JackSuuu/SDP-project-Haloassist/poster/SDP_poster.png

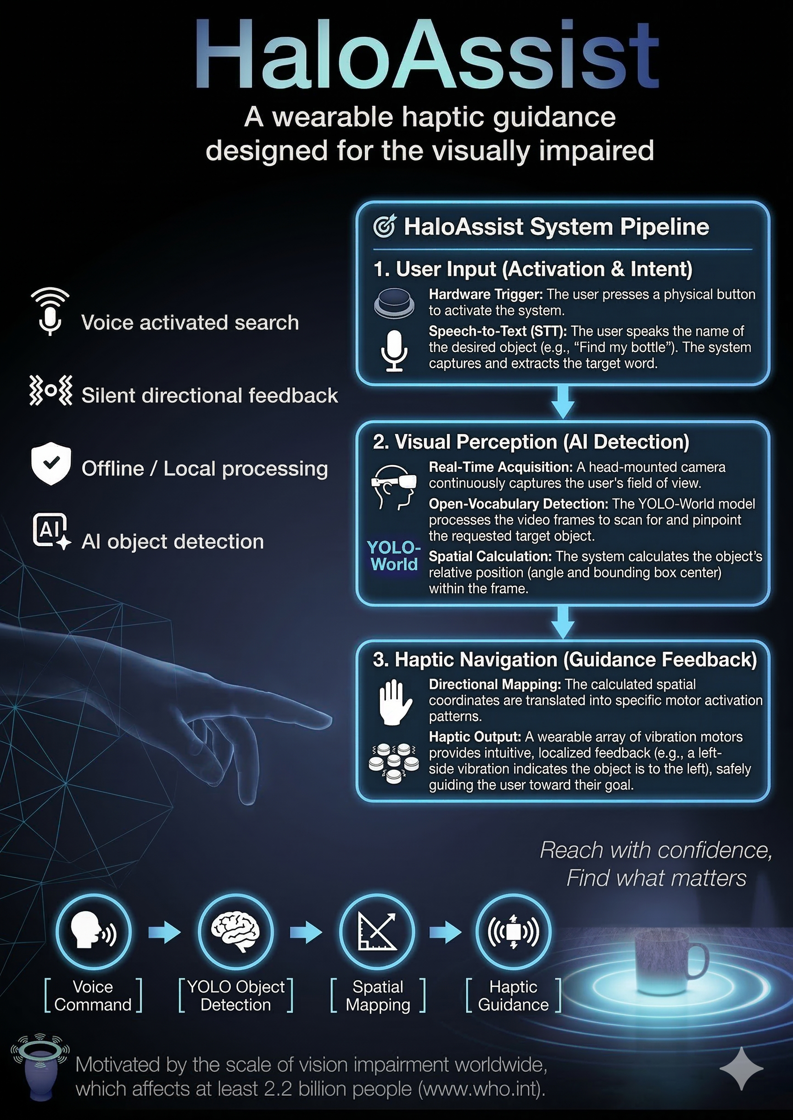
poster/SDP_poster.png
