JackSuuu/SDP-project-Haloassist/Screenshot at 2026-02-09 15-01-05.png

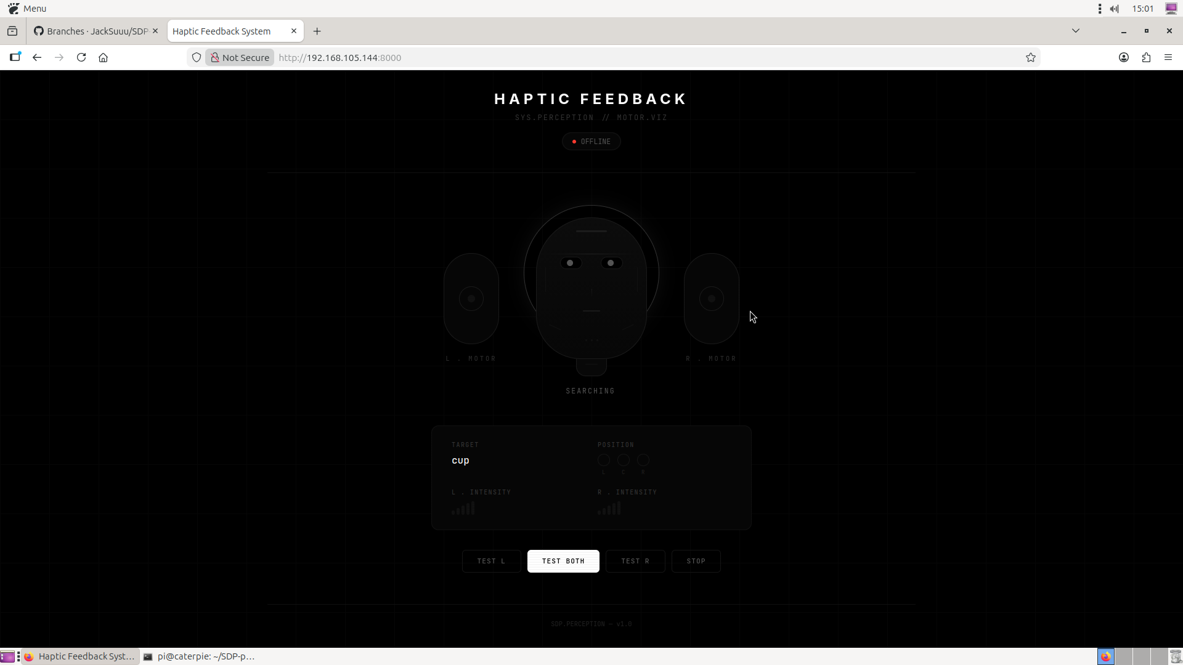
Screenshot at 2026-02-09 15-01-05.png
