JackSuuu/SDP-project-Haloassist/CAD/Fusion360/part_2.stl

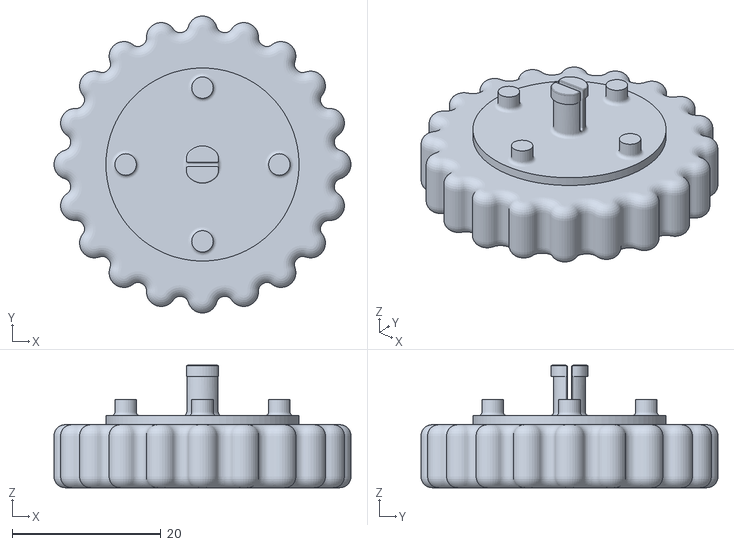
[picture p19: CAD file, 2026-02-28]
CAD/Fusion360/part_2.stl
40.0 x 40.0 x 16.5
