JackSuuu/SDP-project-Haloassist/perception/test_images/apples_near.jpg

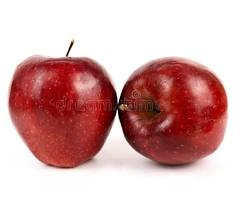
perception/test_images/apples_near.jpg
