JackSuuu/SDP-project-Haloassist/perception/test_images/bottles_in_stands_far.jpg

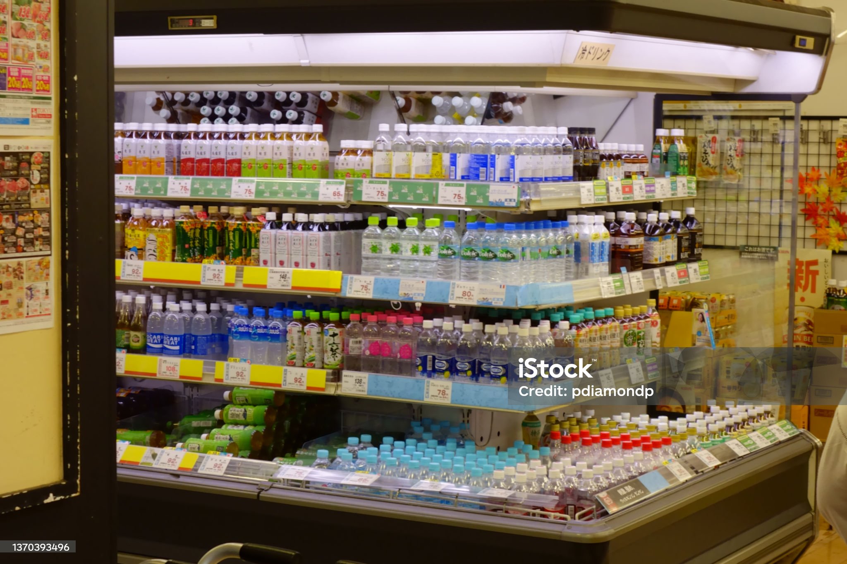
perception/test_images/bottles_in_stands_far.jpg
