JackSuuu/SDP-project-Haloassist/perception/test_images/bottles_in_stands_middle.jpg

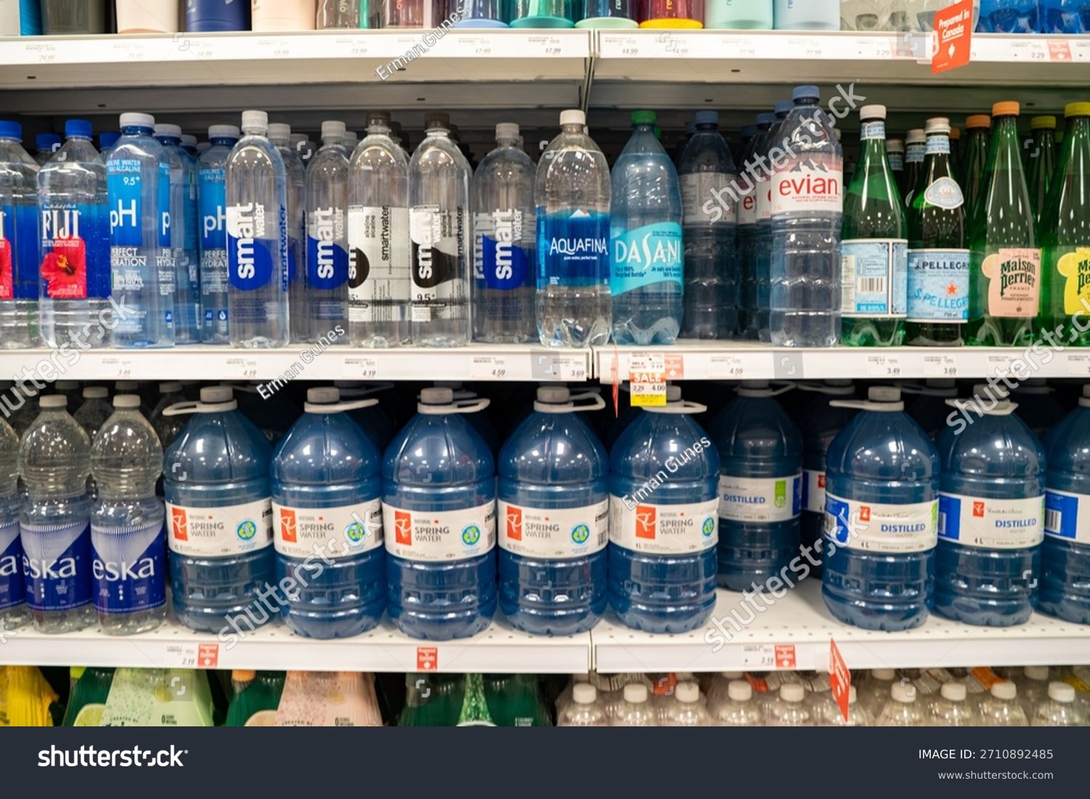
perception/test_images/bottles_in_stands_middle.jpg
