JackSuuu/SDP-project-Haloassist/perception/test_images/bottles_near.jpg

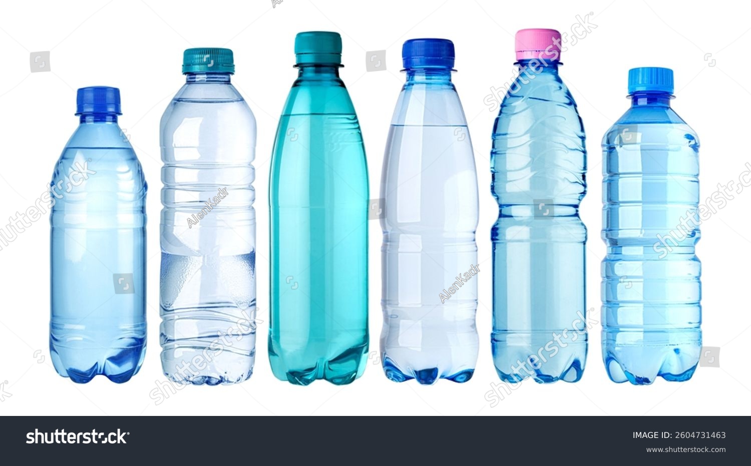
perception/test_images/bottles_near.jpg
