JackSuuu/SDP-project-Haloassist/perception/test_images/broccoli_near.jpg

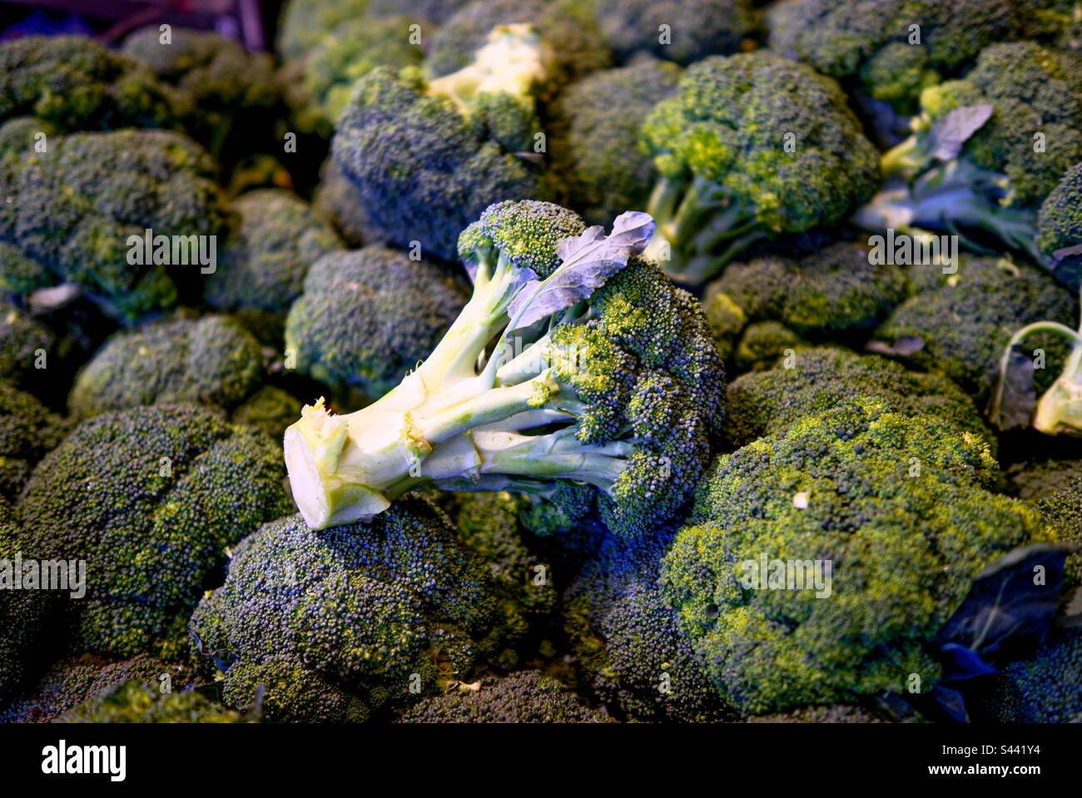
perception/test_images/broccoli_near.jpg
