JackSuuu/SDP-project-Haloassist/perception/test_images/can_boxes_middle.jpg

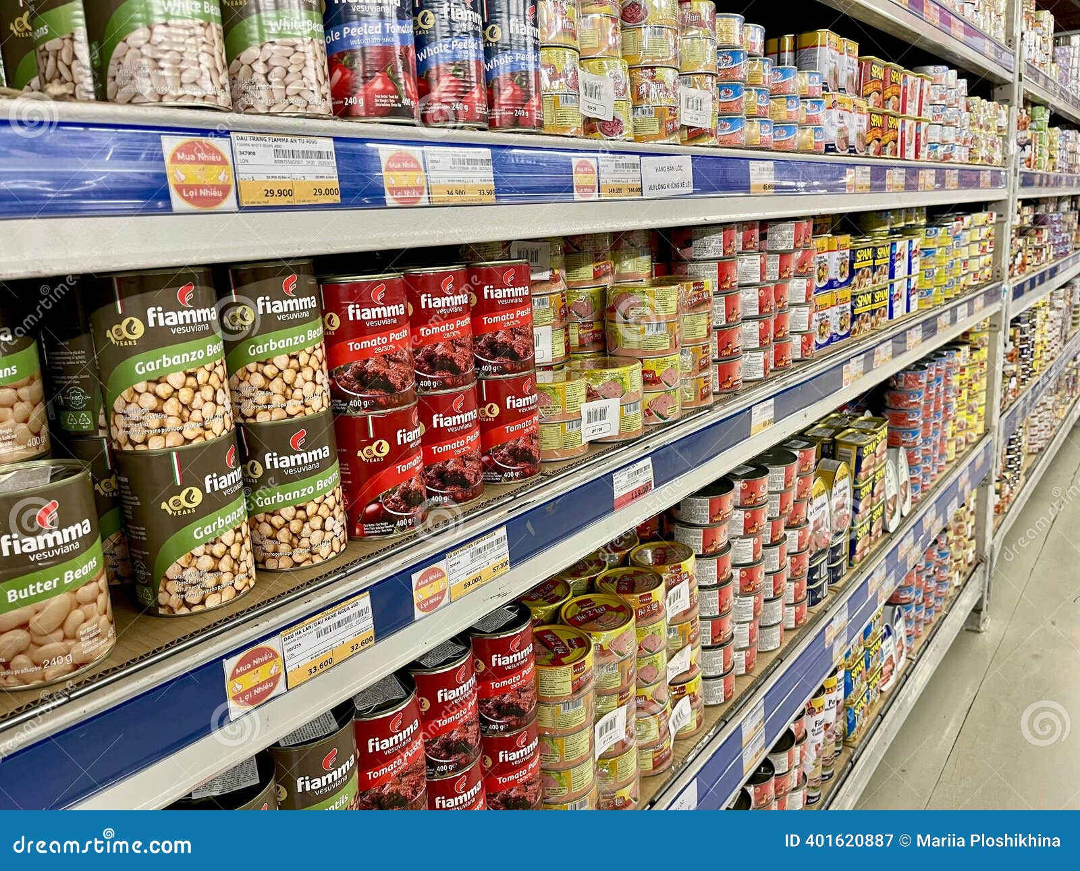
perception/test_images/can_boxes_middle.jpg
