JackSuuu/SDP-project-Haloassist/perception/test_images/chair2.jpg

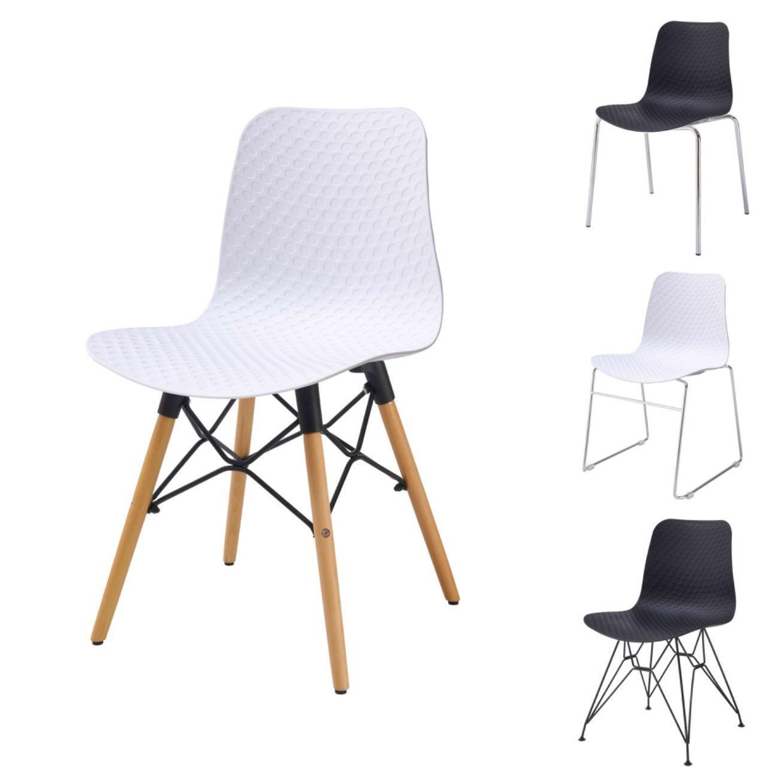
perception/test_images/chair2.jpg
