JackSuuu/SDP-project-Haloassist/perception/test_images/chair4.jpg

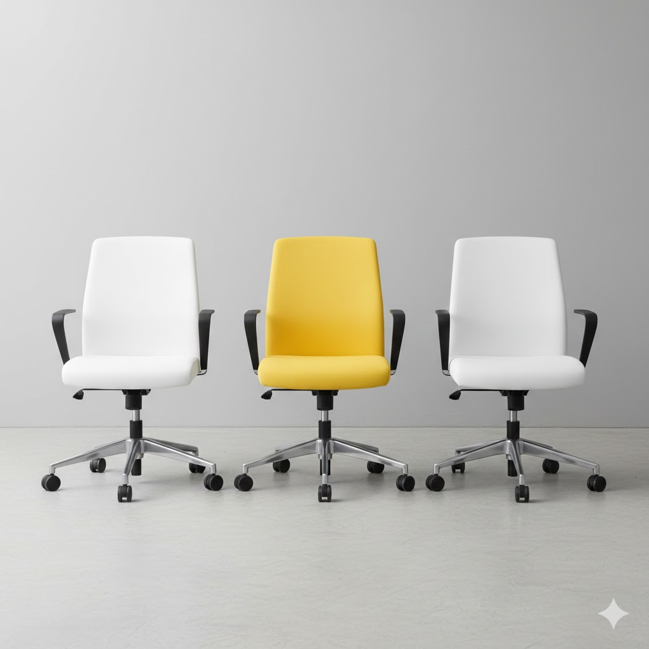
perception/test_images/chair4.jpg
