JackSuuu/SDP-project-Haloassist/perception/test_images/phone_near.jpg

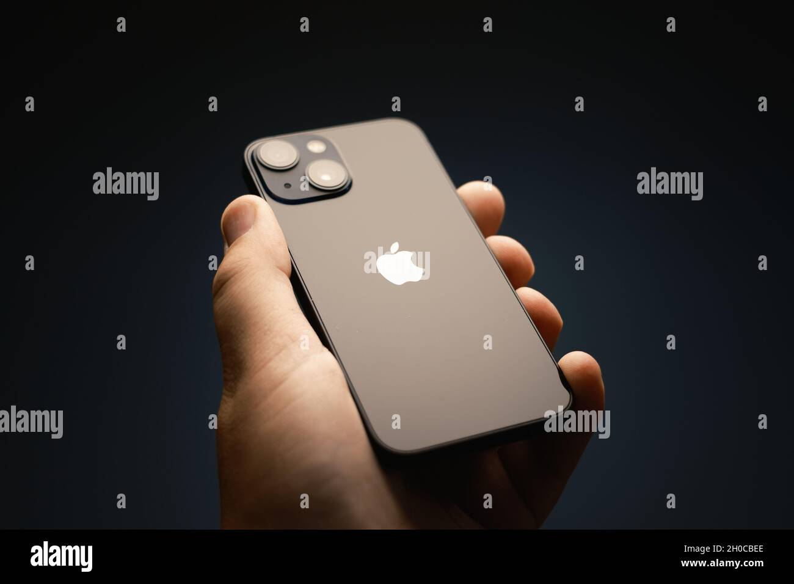
perception/test_images/phone_near.jpg
