JackSuuu/SDP-project-Haloassist/perception/test_images/potato_chip_bags_near.jpg

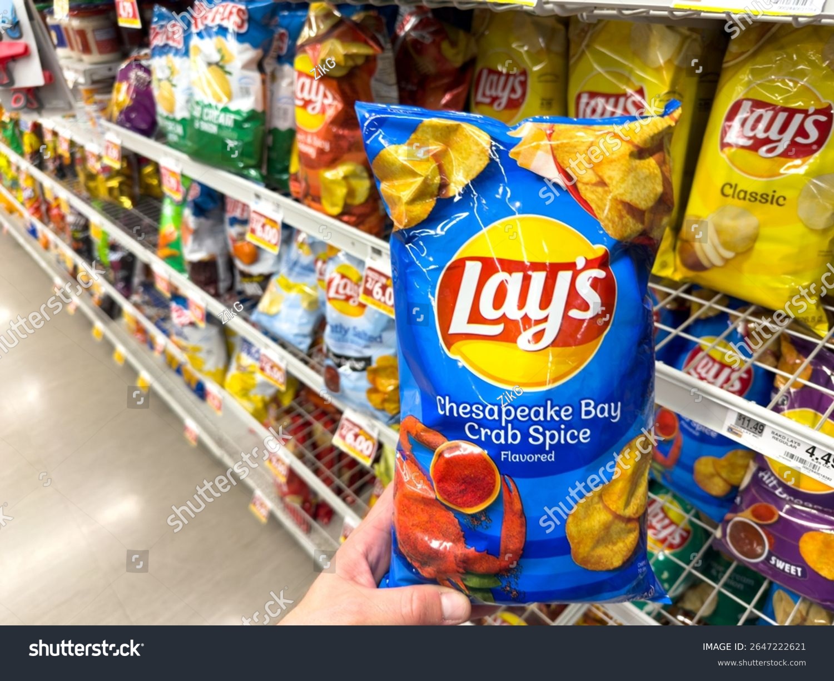
perception/test_images/potato_chip_bags_near.jpg
