JackSuuu/SDP-project-Haloassist/perception/test_images/shampoos_detergent_middle.jpg

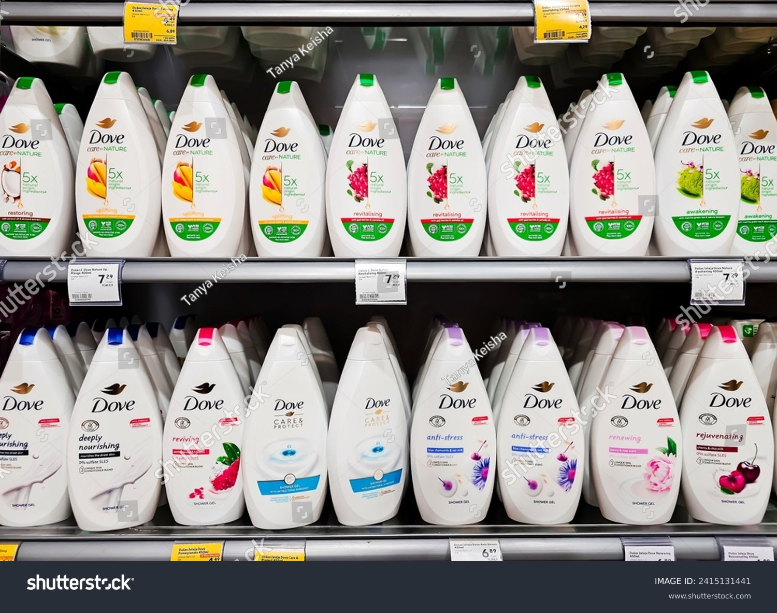
perception/test_images/shampoos_detergent_middle.jpg
