JackSuuu/SDP-project-Haloassist/perception/test_images/suitcase_far.jpg

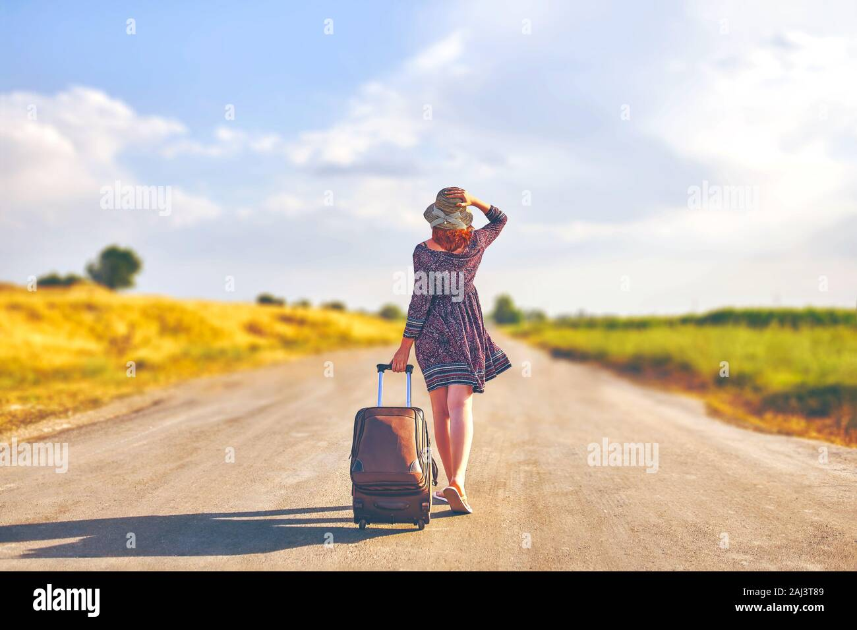
perception/test_images/suitcase_far.jpg
