JackSuuu/SDP-project-Haloassist/test_images/test1.jpeg

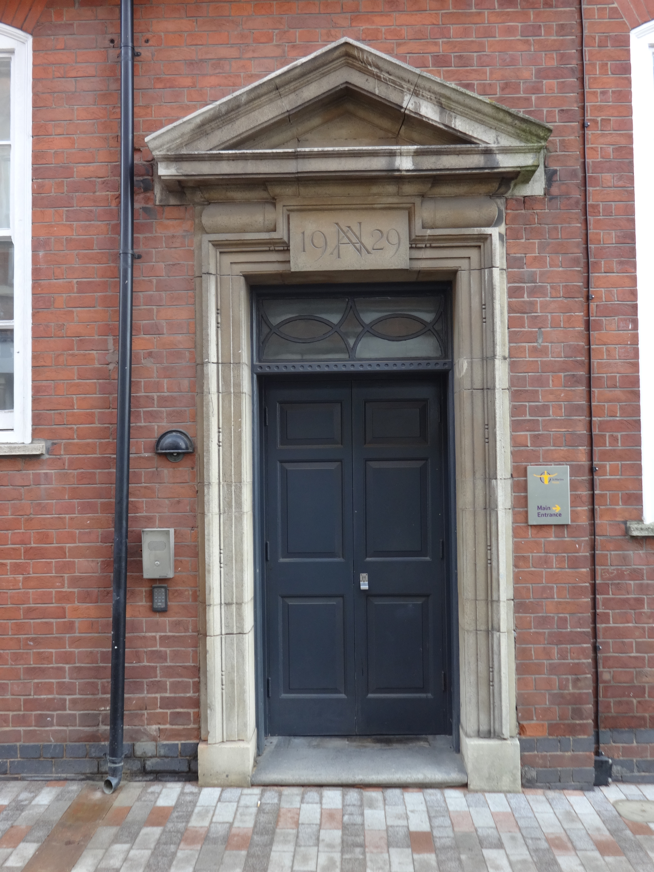
test_images/test1.jpeg
