JackSuuu/SDP-project-Haloassist/test_images/test2.jpeg

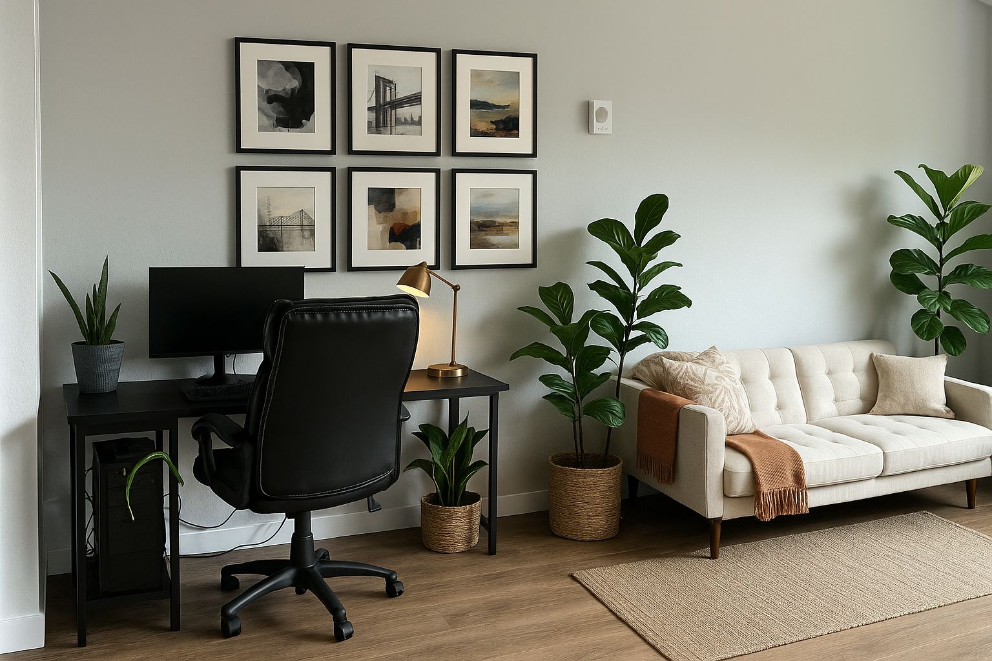
test_images/test2.jpeg
