JackSuuu/SDP-project-Haloassist/test_images/test3.jpeg

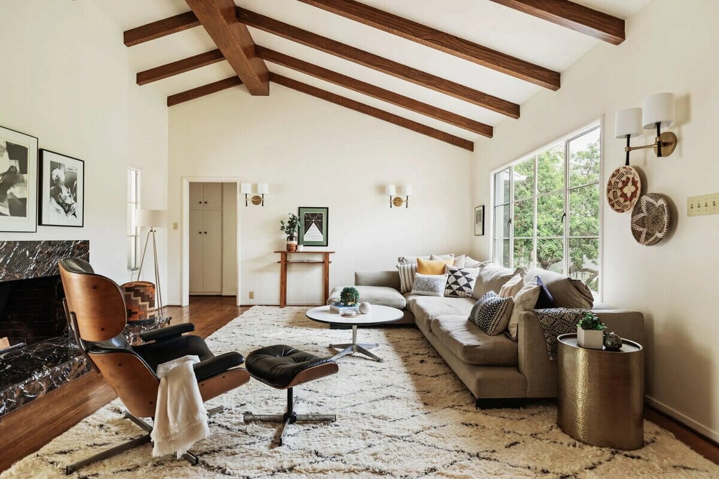
test_images/test3.jpeg
