JackSuuu/SDP-project-Haloassist/test_images/test4.jpeg

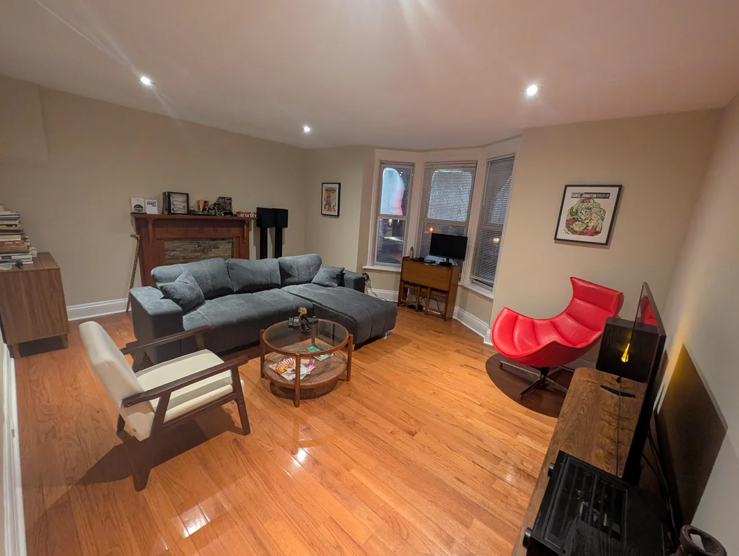
test_images/test4.jpeg
