JackSuuu/SDP-project-Haloassist/test_images/test5.jpeg

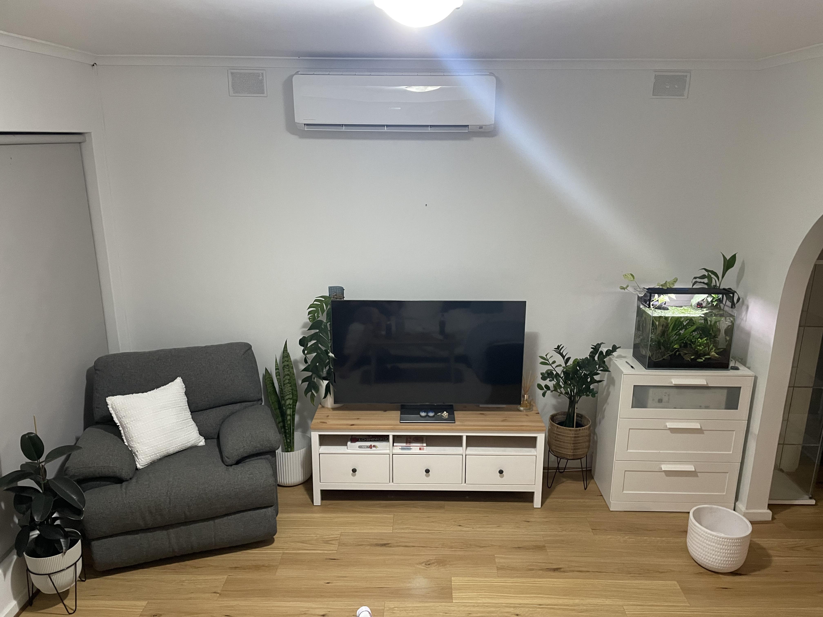
test_images/test5.jpeg
