JackSuuu/SDP-project-Haloassist/test_images/test6.jpeg

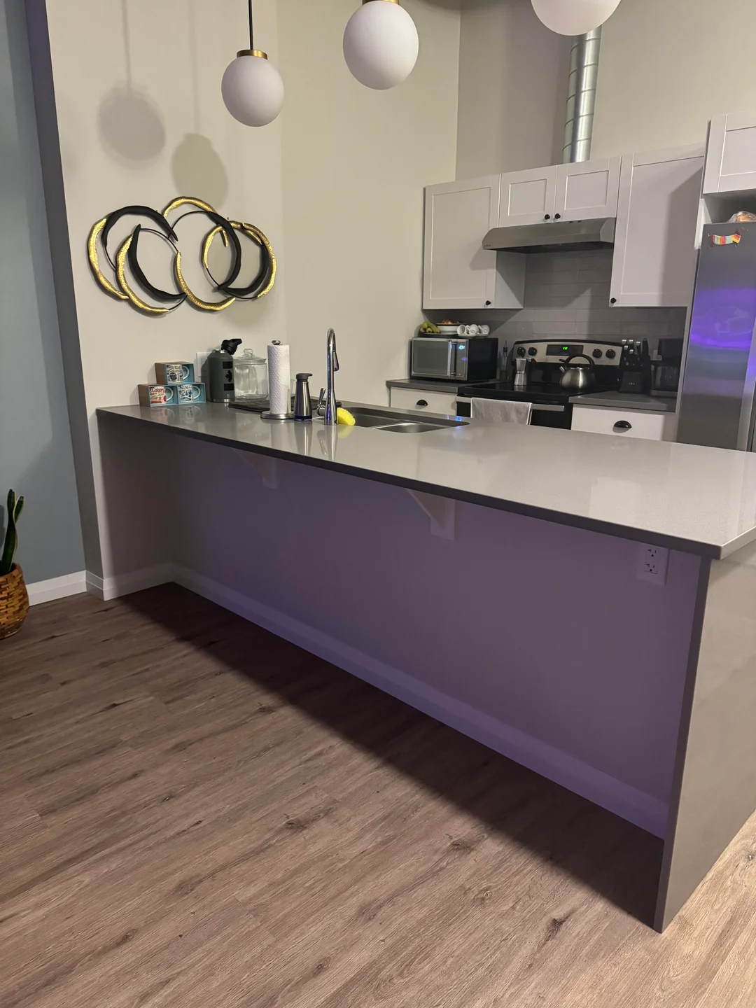
test_images/test6.jpeg
