JackSuuu/SDP-project-Haloassist/test_images/test7.jpeg

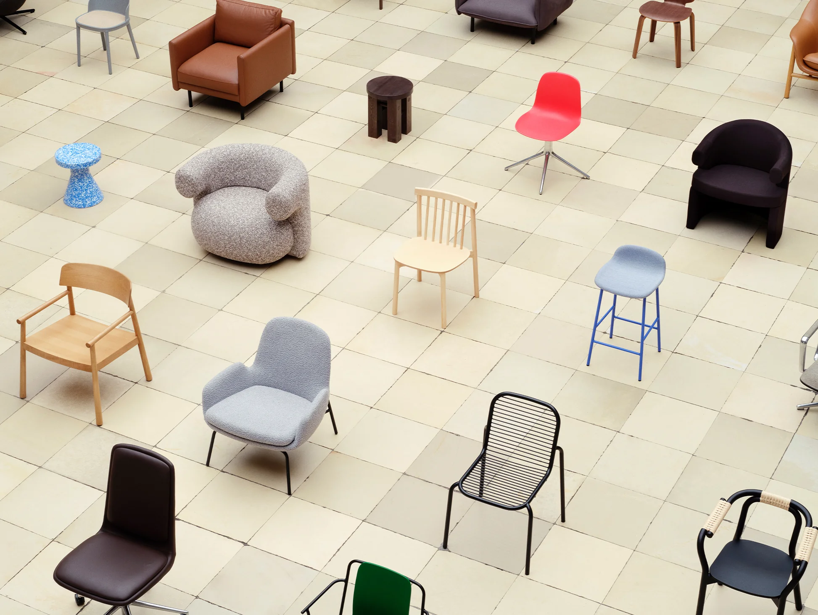
test_images/test7.jpeg
