JackSuuu/SDP-project-Haloassist/test_images/test8.jpeg

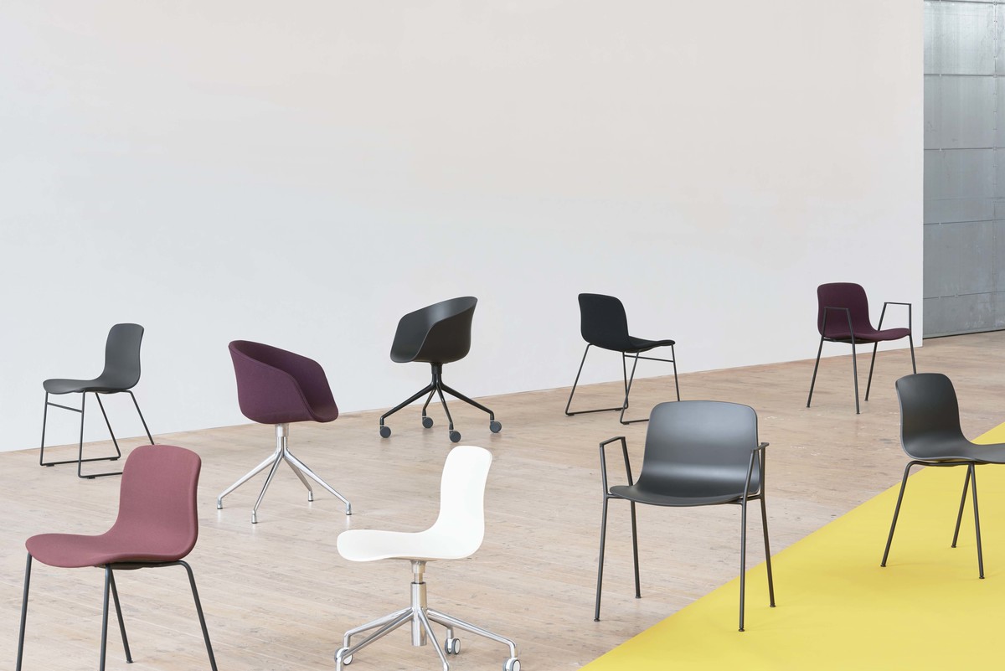
test_images/test8.jpeg
