JackSuuu/SDP-project-Haloassist/test_images/test10.jpeg

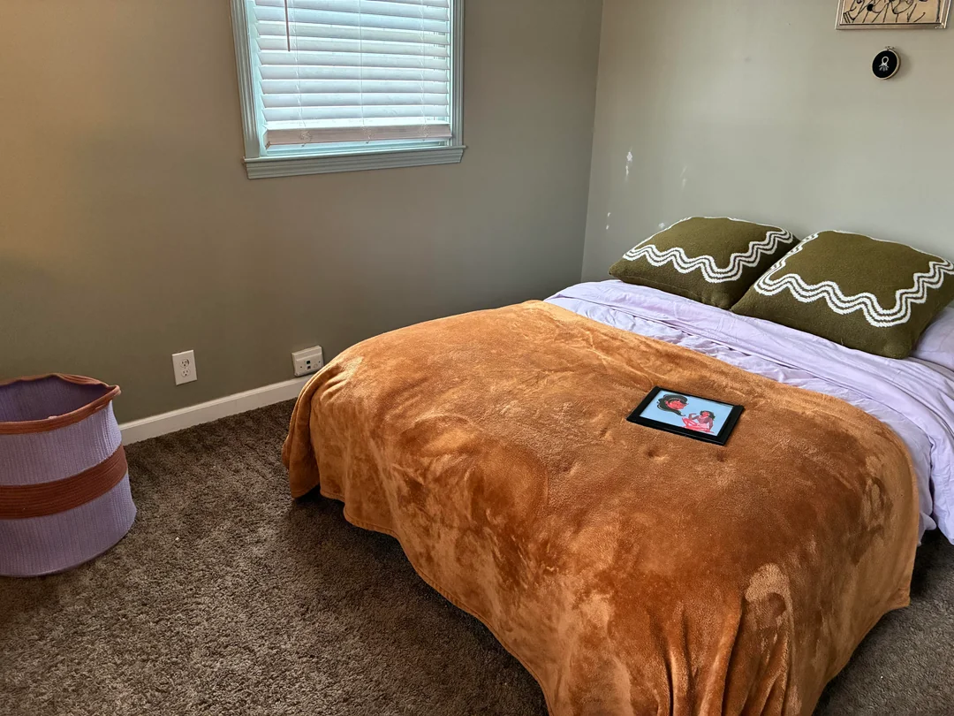
test_images/test10.jpeg
