JackSuuu/SDP-project-Haloassist/test_images/test11.jpeg

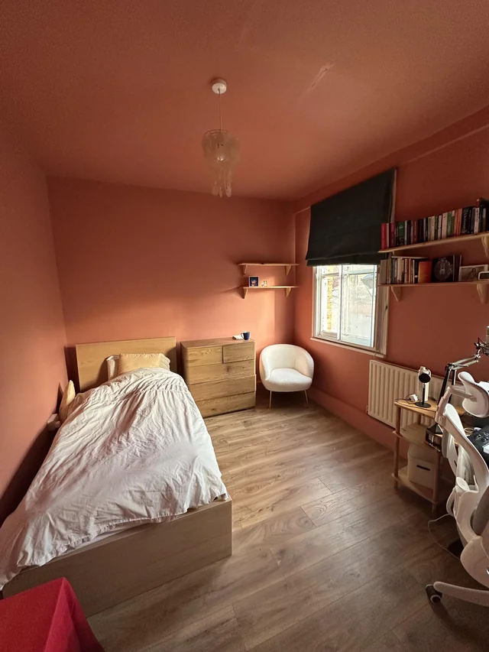
test_images/test11.jpeg
