JackSuuu/SDP-project-Haloassist/HaloAssistV2-backup/testSpeaker.py

from speaker import Speaker

spk = Speaker()

spk.beep(440, 0.2, 0.4)
spk.success()
spk.error()
spk.alert()
spk.success()
spk.speak("First Configured.")
spk.success()
spk.speak("Second Configured.")
spk.success()
spk.speak("Third Configured.")
spk.success()
